mavro10600/Finder/catkin_et/src/roswww/www/img/temp/cPatternDetected1.30780159511.jpg

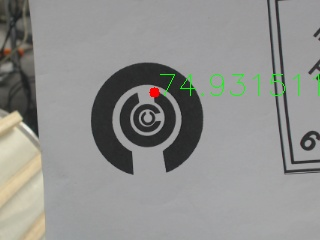
catkin_et/src/roswww/www/img/temp/cPatternDetected1.30780159511.jpg
