mavro10600/Finder/catkin_et/src/roswww/www/img/temp/cPatternDetected1.50422816302.jpg

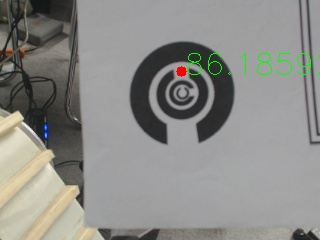
catkin_et/src/roswww/www/img/temp/cPatternDetected1.50422816302.jpg
