mavro10600/Finder/catkin_et/src/roswww/www/img/temp/cPatternDetected1.57079632679.jpg

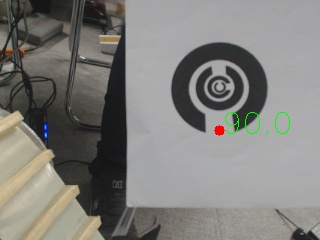
catkin_et/src/roswww/www/img/temp/cPatternDetected1.57079632679.jpg
