mavro10600/Finder/catkin_et/src/roswww/www/img/temp/cPatternDetected1.61159000966.jpg

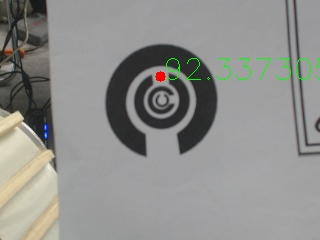
catkin_et/src/roswww/www/img/temp/cPatternDetected1.61159000966.jpg
