mavro10600/Finder/catkin_et/src/roswww/www/img/temp/cPatternDetected4.73537343783.jpg

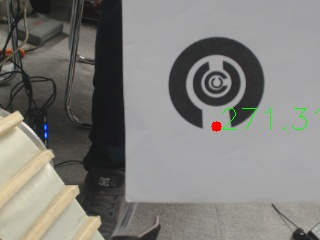
catkin_et/src/roswww/www/img/temp/cPatternDetected4.73537343783.jpg
