mavro10600/Finder/catkin_et/src/vision/labels_hazmate_detector/scripts/hlabel/cartridge_pic_1.png

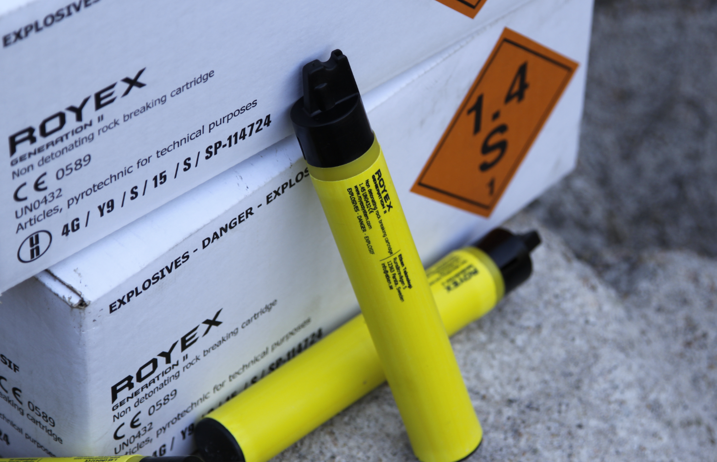
catkin_et/src/vision/labels_hazmate_detector/scripts/hlabel/cartridge_pic_1.png
