mavro10600/Finder/catkin_et/src/vision/labels_hazmate_detector/scripts/hlabel/colorYcrcb.bmp

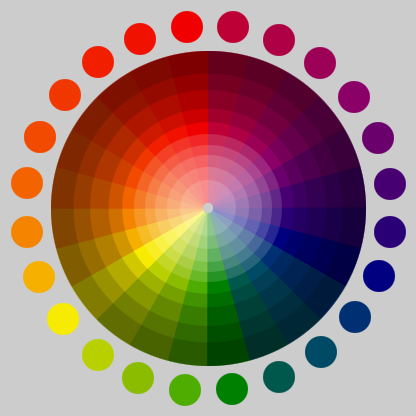
catkin_et/src/vision/labels_hazmate_detector/scripts/hlabel/colorYcrcb.bmp
