mavro10600/Finder/catkin_et/src/vision/labels_hazmate_detector/scripts/hlabel/dan_when_we.jpg

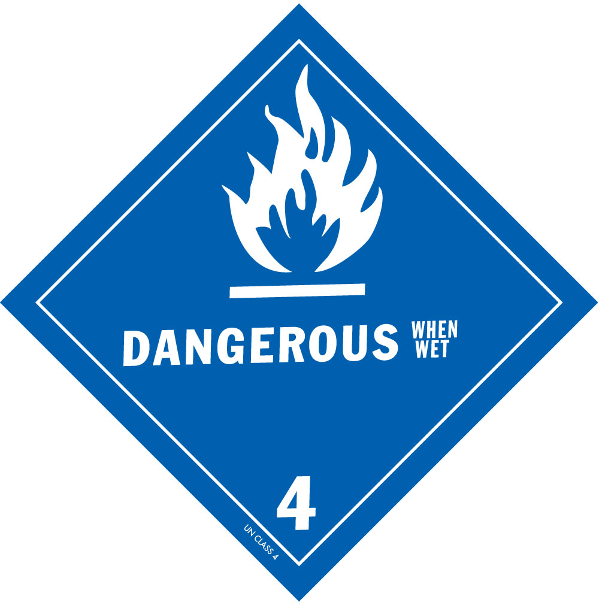
catkin_et/src/vision/labels_hazmate_detector/scripts/hlabel/dan_when_we.jpg
