mavro10600/Finder/catkin_et/src/vision/labels_hazmate_detector/scripts/hlabel/dan_when_weh.JPG

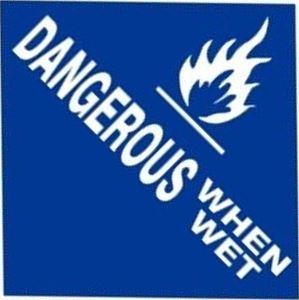
catkin_et/src/vision/labels_hazmate_detector/scripts/hlabel/dan_when_weh.JPG
