mavro10600/Finder/catkin_et/src/vision/labels_hazmate_detector/scripts/hlabel/explosh.jpg

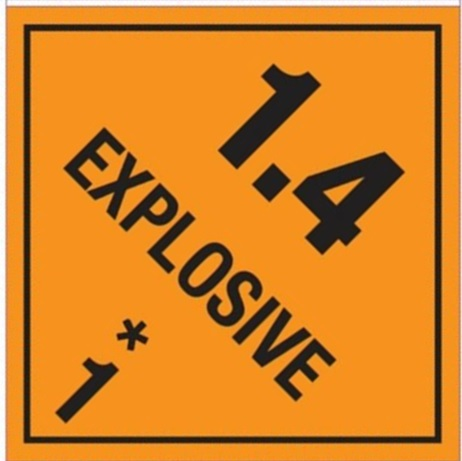
catkin_et/src/vision/labels_hazmate_detector/scripts/hlabel/explosh.jpg
