mavro10600/Finder/catkin_et/src/vision/labels_hazmate_detector/scripts/hlabel/flam_gas2.jpg

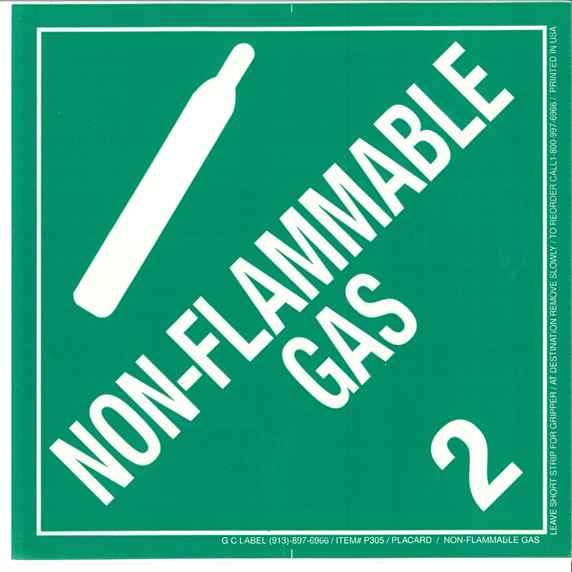
catkin_et/src/vision/labels_hazmate_detector/scripts/hlabel/flam_gas2.jpg
