mavro10600/Finder/catkin_et/src/vision/labels_hazmate_detector/scripts/hlabel/flam_liqh.JPG

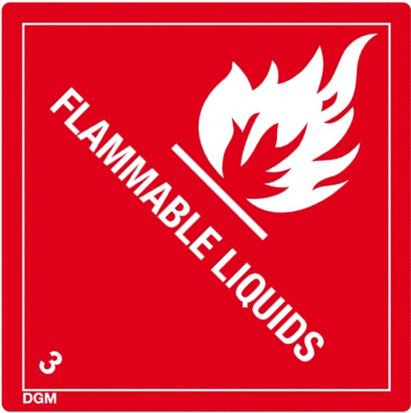
catkin_et/src/vision/labels_hazmate_detector/scripts/hlabel/flam_liqh.JPG
