mavro10600/Finder/catkin_et/src/vision/labels_hazmate_detector/scripts/hlabel/flamm_liqu.jpg

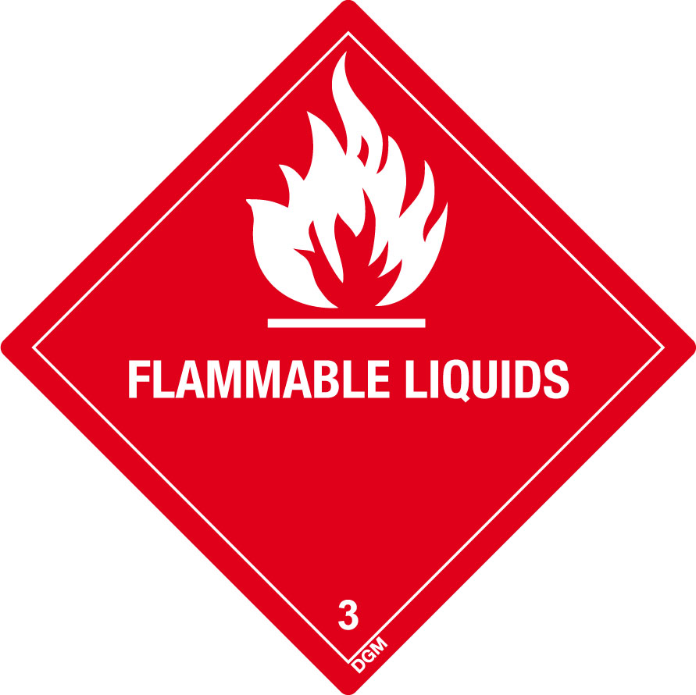
catkin_et/src/vision/labels_hazmate_detector/scripts/hlabel/flamm_liqu.jpg
