mavro10600/Finder/catkin_et/src/vision/labels_hazmate_detector/scripts/hlabel/inha_haz.jpg

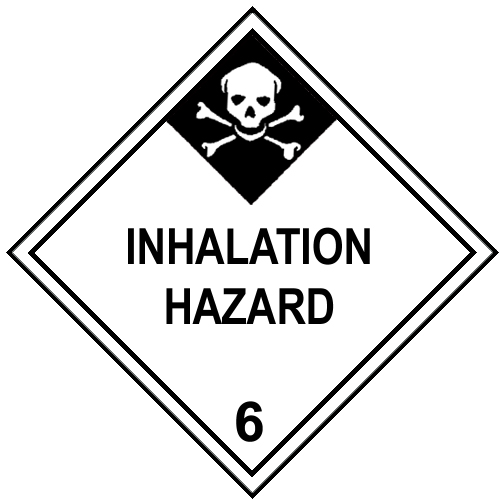
catkin_et/src/vision/labels_hazmate_detector/scripts/hlabel/inha_haz.jpg
