mavro10600/Finder/catkin_et/src/vision/labels_hazmate_detector/scripts/hlabel/mano.png

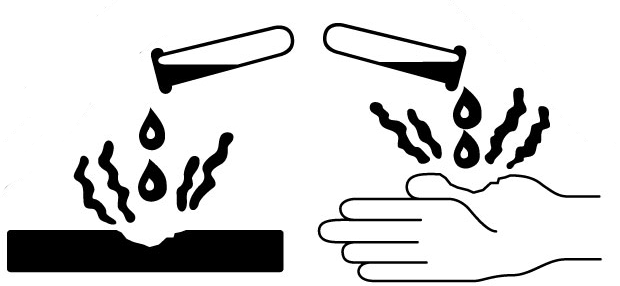
catkin_et/src/vision/labels_hazmate_detector/scripts/hlabel/mano.png
