mavro10600/Finder/catkin_et/src/vision/labels_hazmate_detector/scripts/hlabel/organ_peroxh.JPG

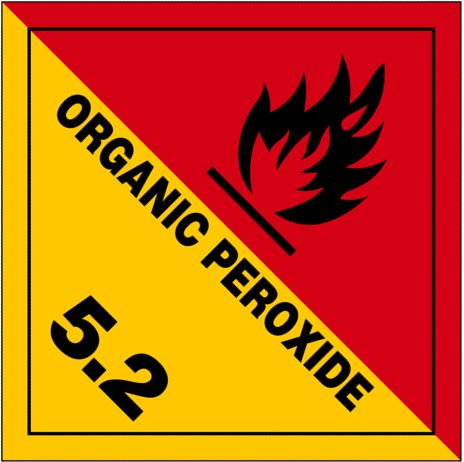
catkin_et/src/vision/labels_hazmate_detector/scripts/hlabel/organ_peroxh.JPG
