mavro10600/Finder/catkin_et/src/vision/labels_hazmate_detector/scripts/hlabel/radioh.JPG

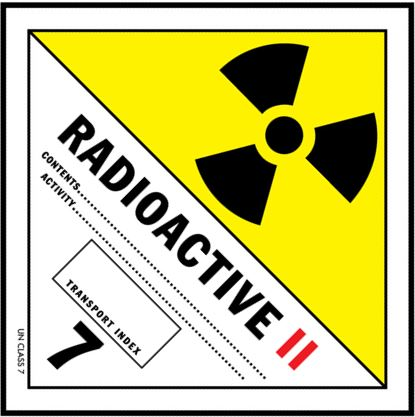
catkin_et/src/vision/labels_hazmate_detector/scripts/hlabel/radioh.JPG
