mavro10600/Finder/catkin_et/src/vision/labels_hazmate_detector/scripts/hlabel/spon_combh.JPG

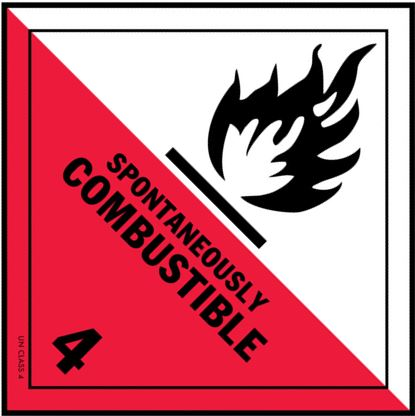
catkin_et/src/vision/labels_hazmate_detector/scripts/hlabel/spon_combh.JPG
