mavro10600/Finder/catkin_et/src/vision/labels_hazmate_detector/scripts/patternsBl/pat2.jpg

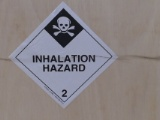
catkin_et/src/vision/labels_hazmate_detector/scripts/patternsBl/pat2.jpg
