mavro10600/Finder/catkin_et/src/vision/labels_hazmate_detector/scripts/patternsBl/pat3.jpg

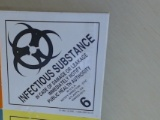
catkin_et/src/vision/labels_hazmate_detector/scripts/patternsBl/pat3.jpg
