mavro10600/Finder/catkin_et/src/vision/labels_hazmate_detector/scripts/patternsRed/pat1.jpg

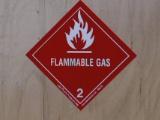
catkin_et/src/vision/labels_hazmate_detector/scripts/patternsRed/pat1.jpg
