mavro10600/Finder/catkin_et/src/vision/labels_hazmate_detector/scripts/patternsRed/pat4.jpg

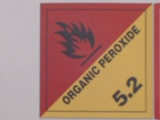
catkin_et/src/vision/labels_hazmate_detector/scripts/patternsRed/pat4.jpg
