mavro10600/Finder/catkin_et/src/finder_description/meshes_2/flipper_lf.obj

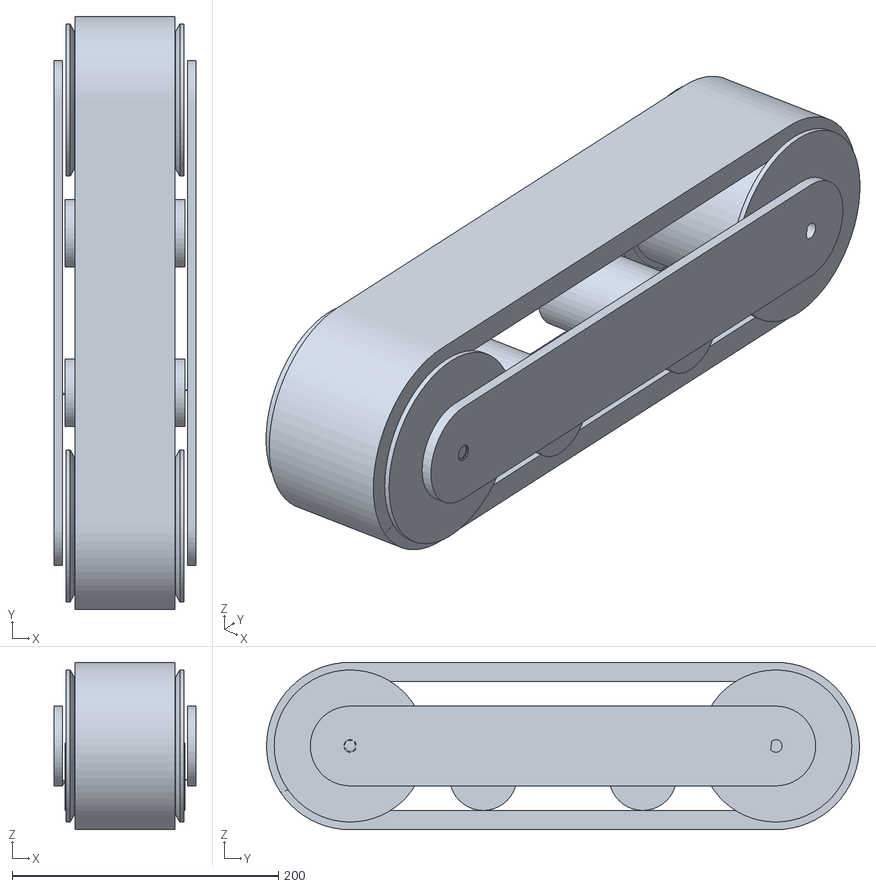
[picture p87: CAD file, 2017-04-17]
catkin_et/src/finder_description/meshes_2/flipper_lf.obj
106.6 x 445.9 x 125.9
