mavro10600/Finder/catkin_et/src/config_files/meshes/chasis.obj

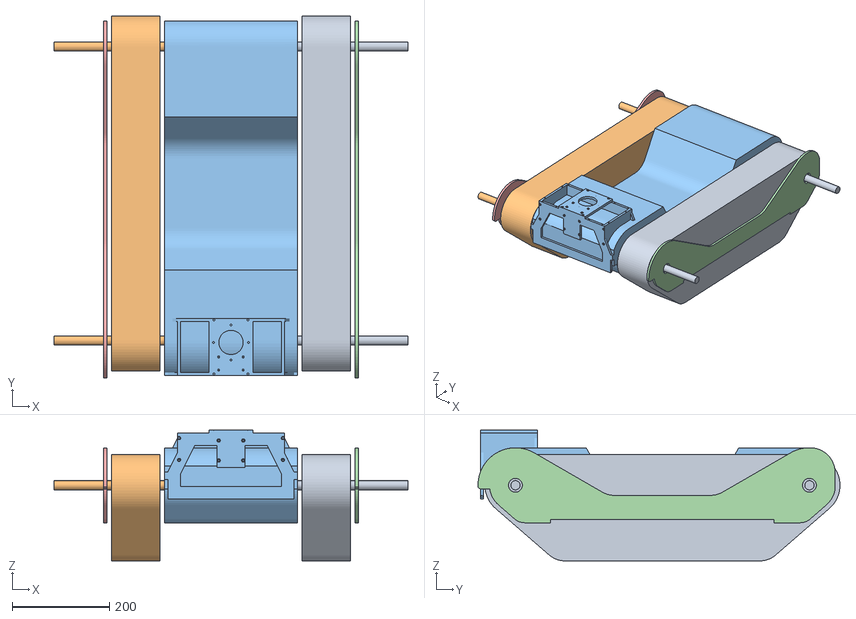
[picture p88: CAD file, 2017-04-17]
catkin_et/src/config_files/meshes/chasis.obj
727.8 x 745.0 x 269.1
