mavro10600/Finder/catkin_et/src/finder_description/mallas/yaw.obj

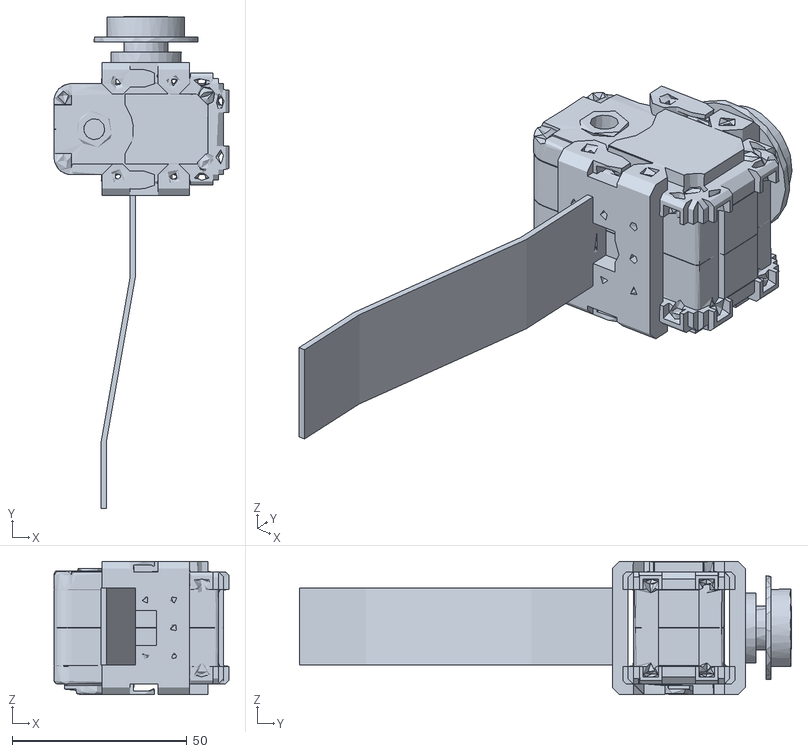
[picture p89: CAD file, 2017-05-09]
catkin_et/src/finder_description/mallas/yaw.obj
50.0 x 140.6 x 38.1
