mavro10600/Finder/catkin_et/src/finder_description/meshes_2/flipper_rb.obj

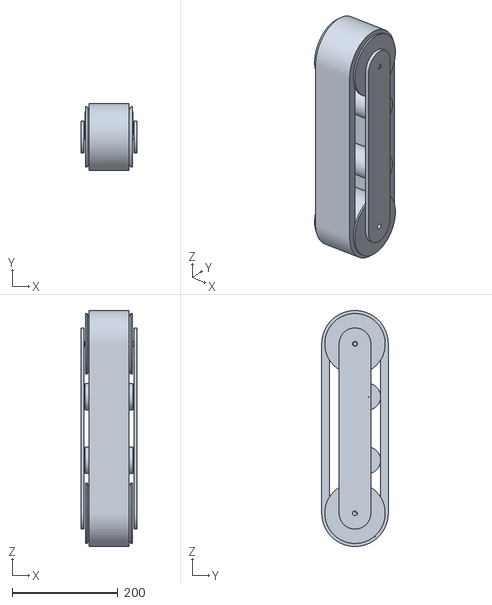
[picture p91: CAD file, 2017-04-17]
catkin_et/src/finder_description/meshes_2/flipper_rb.obj
106.6 x 125.9 x 445.9
