mavro10600/Finder/catkin_et/src/finder_description/meshes_light/pitch_light.obj

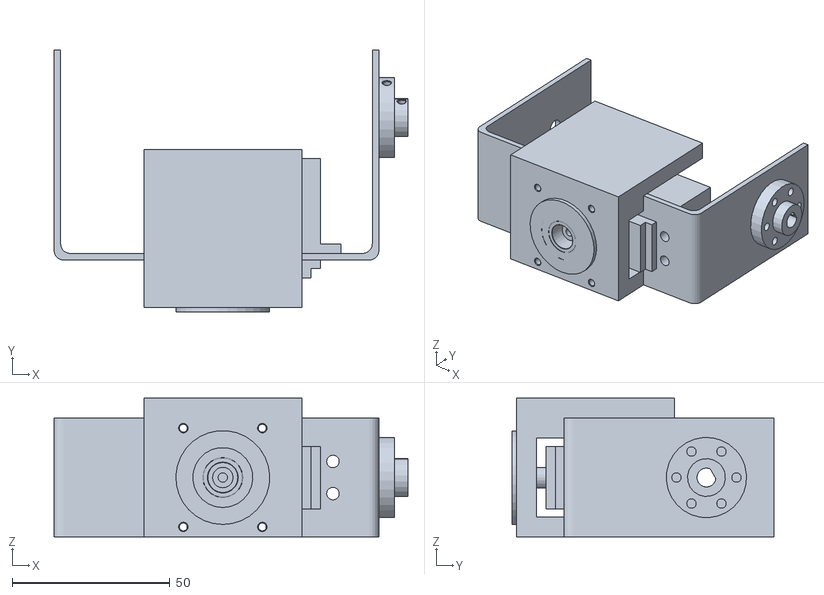
[picture p92: CAD file, 2017-04-17]
catkin_et/src/finder_description/meshes_light/pitch_light.obj
112.0 x 83.0 x 44.0
