mavro10600/Finder/catkin_et/src/finder_description/mallas/roll1.obj

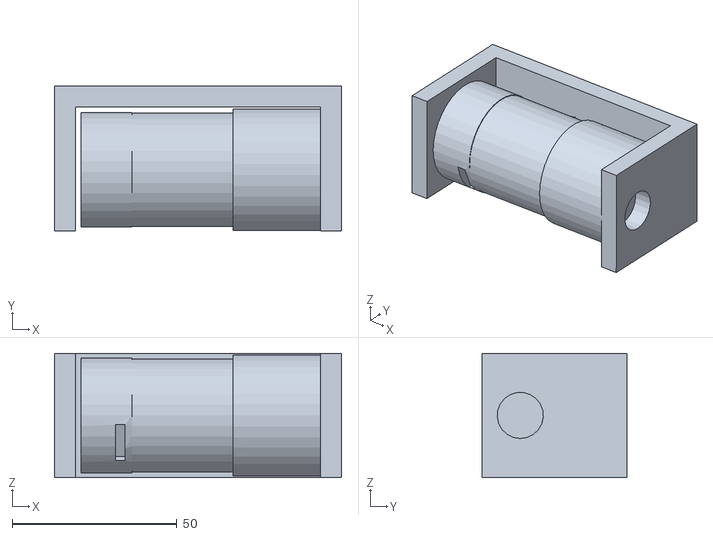
[picture p93: CAD file, 2017-05-09]
catkin_et/src/finder_description/mallas/roll1.obj
87.0 x 44.0 x 37.7
