mavro10600/Finder/catkin_et/src/finder_description/meshes_2/codo.obj

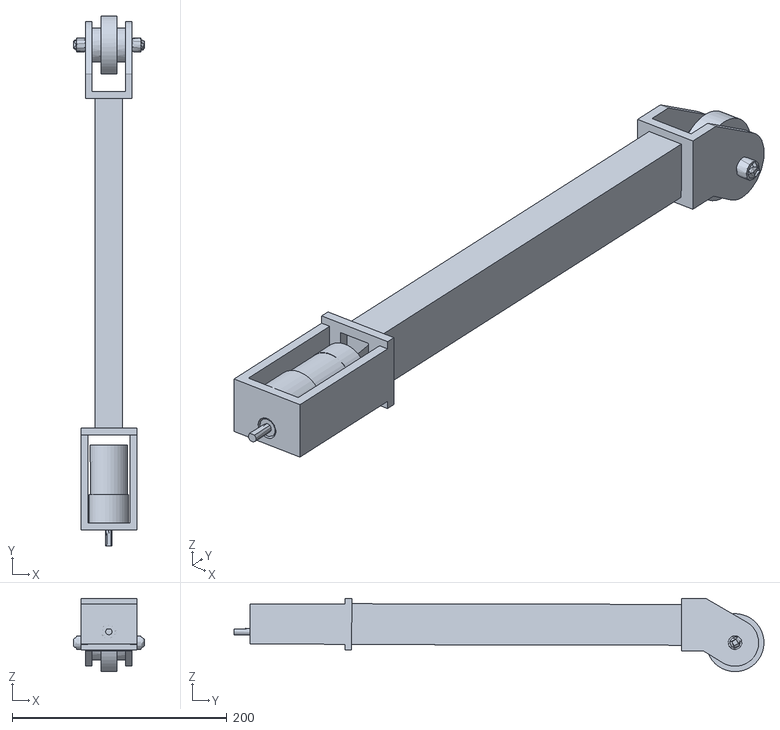
[picture p94: CAD file, 2017-04-17]
catkin_et/src/finder_description/meshes_2/codo.obj
66.0 x 494.0 x 68.3
