mavro10600/Finder/catkin_et/src/config_files/meshes/base.stl

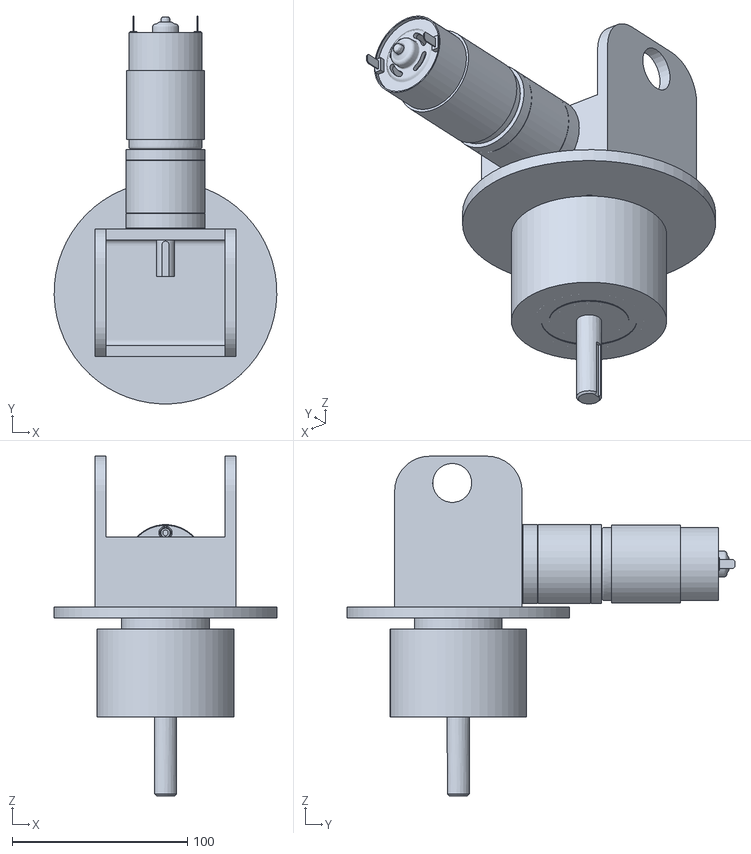
[picture p95: CAD file, 2017-04-17]
catkin_et/src/config_files/meshes/base.stl
127.0 x 221.3 x 193.7
