mavro10600/Finder/catkin_et/src/finder_description/meshes_light/hombro.obj

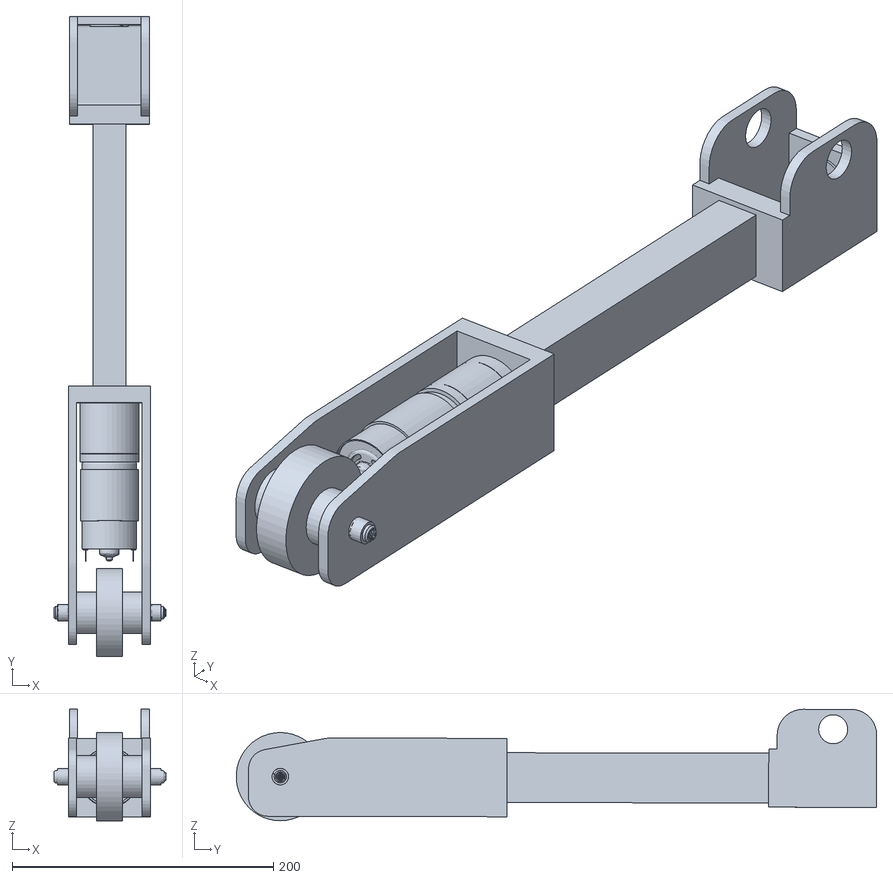
[picture p96: CAD file, 2017-04-17]
catkin_et/src/finder_description/meshes_light/hombro.obj
85.7 x 490.0 x 85.3
