mavro10600/Finder/catkin_et/src/config_files/meshes/roll _1.stl

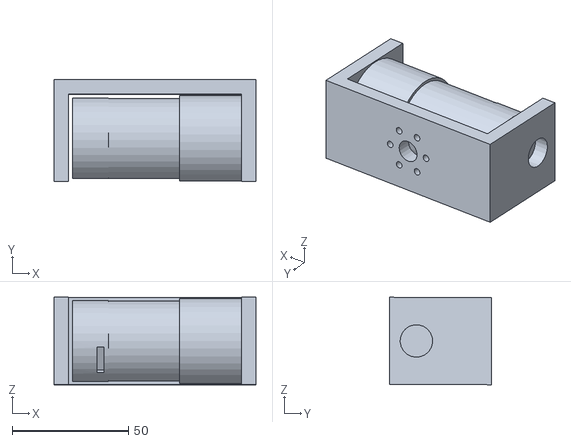
[picture p97: CAD file, 2017-04-17]
catkin_et/src/config_files/meshes/roll _1.stl
87.0 x 44.0 x 37.7
