mavro10600/Finder/catkin_et/src/finder_description/mallas/fingers.obj

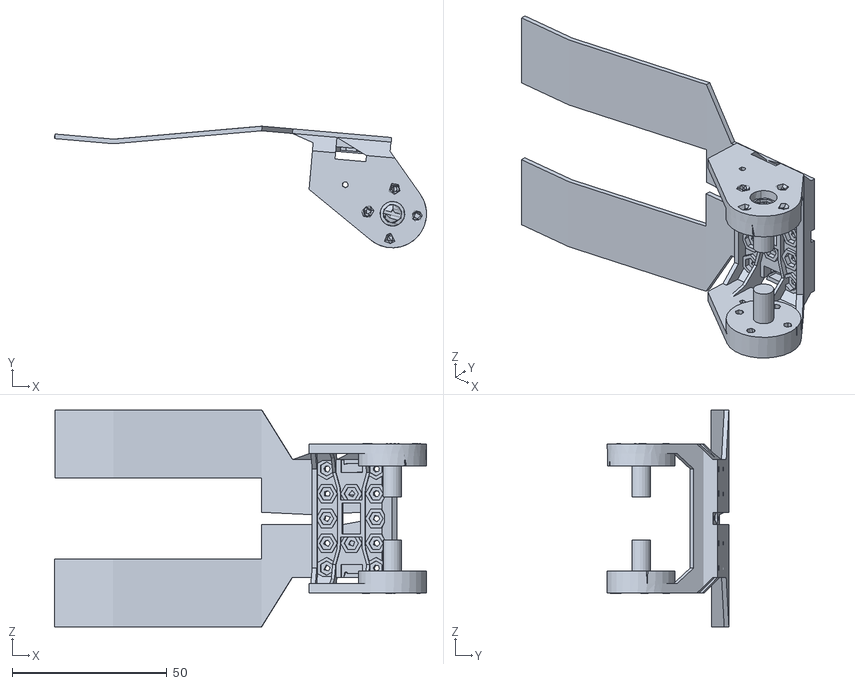
[picture p98: CAD file, 2017-05-09]
catkin_et/src/finder_description/mallas/fingers.obj
120.1 x 39.3 x 70.0
