mavro10600/Finder/catkin_et/src/finder_description/mallas/codo.stl

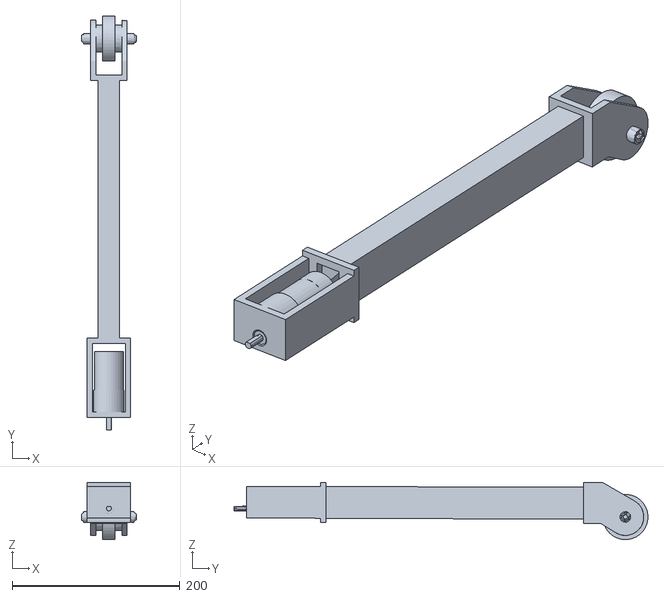
[picture p99: CAD file, 2017-05-09]
catkin_et/src/finder_description/mallas/codo.stl
66.0 x 494.0 x 68.3
