mavro10600/Finder/catkin_et/src/vision/labels_hazmate_detector/scripts/hlabel/flammLiquTest2.png

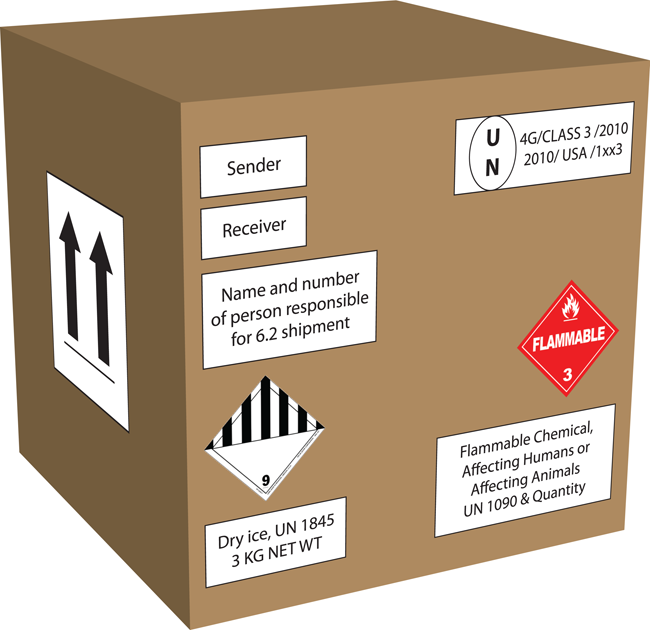
catkin_et/src/vision/labels_hazmate_detector/scripts/hlabel/flammLiquTest2.png
