mavro10600/Finder/catkin_et/src/vision/labels_hazmate_detector/scripts/hlabel/testHaz2(1).JPG

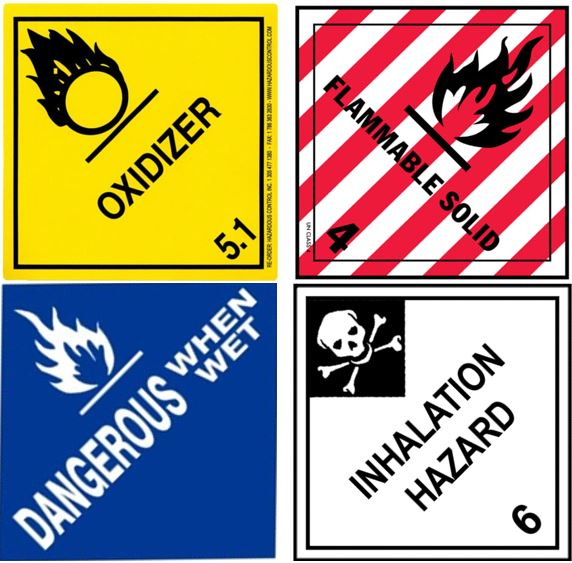
catkin_et/src/vision/labels_hazmate_detector/scripts/hlabel/testHaz2(1).JPG
