mavro10600/Finder/catkin_et/src/vision/labels_hazmate_detector/scripts/hlabel/testHaz3.png

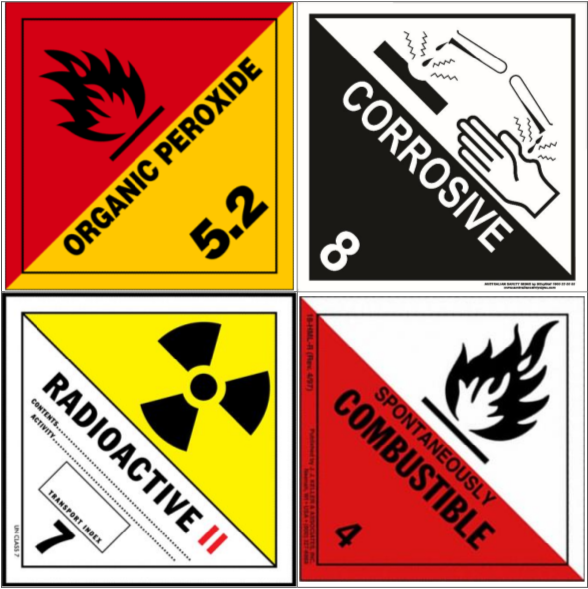
catkin_et/src/vision/labels_hazmate_detector/scripts/hlabel/testHaz3.png
