mavro10600/Finder/catkin_et/src/vision/labels_hazmate_detector/scripts/hlabel/hazard_labels2.png

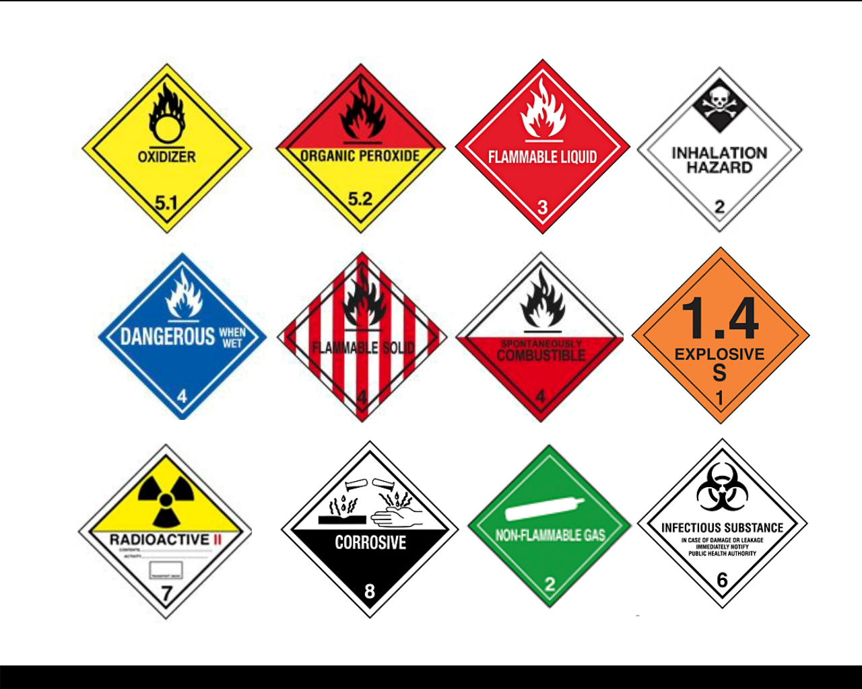
catkin_et/src/vision/labels_hazmate_detector/scripts/hlabel/hazard_labels2.png
