mavro10600/Finder/sketchbook/pruebas_roboclaw/pruebas_roboclaw.ino

//See BareMinimum example for a list of library functions

//Includes required to use Roboclaw library
#include <SoftwareSerial.h>
#include "RoboClaw.h"

//See limitations of Arduino SoftwareSerial
SoftwareSerial serial(10,11);	
RoboClaw roboclaw(&serial,10000);

#define address 0x80

void setup() {
  //Open Serial and roboclaw at 38400bps
  Serial.begin(57600);
  roboclaw.begin(9600);
}

void loop() {
  uint8_t status1,status2,status3,status4;
  bool valid1,valid2,valid3,valid4;
  uint16_t configuracion;
  //Read all the data from Roboclaw before displaying on Serial Monitor window
  //This prevents the hardware serial interrupt from interfering with
  //reading data using software serial.
  int32_t enc1= roboclaw.ReadEncM1(address, &status1, &valid1);
  valid2=roboclaw.GetConfig(address, configuracion);
  //bool ReadEncoderModes(uint8_t address, uint8_t &M1mode, uint8_t &M2mode);
  
  
  if(valid1){
    Serial.print(enc1,HEX);
    Serial.print(" ");
    Serial.print(status1,HEX);
    Serial.print(" ");
  }
  else{
    Serial.print("invalid ");
  }
  
  if(valid2){


    Serial.print(configuracion,HEX);
    Serial.println(" ");
  }
  else{
    Serial.print("invalida ");
  }
  
  delay(100);
}
